00Lyun00/Charybdis-Nano-Buildlog/Buildlog/Images/13.jpg

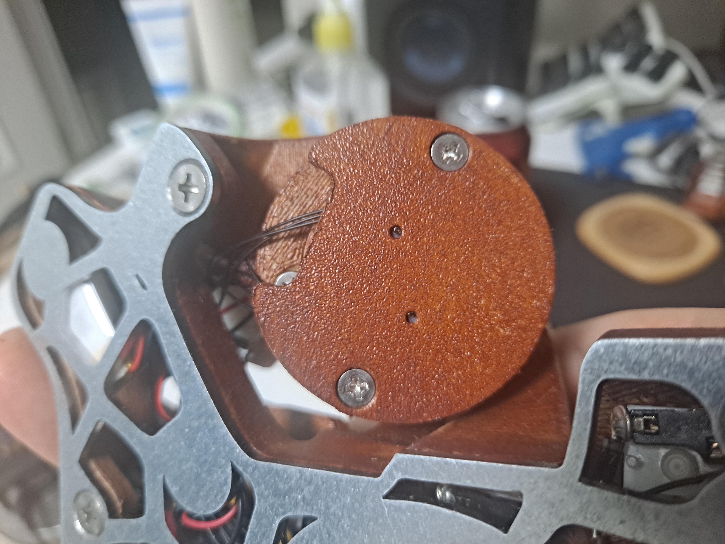
Buildlog/Images/13.jpg
